GraemePerrins/LEDLamp/FinishedLamp/PXL_20251227_023226788.jpg

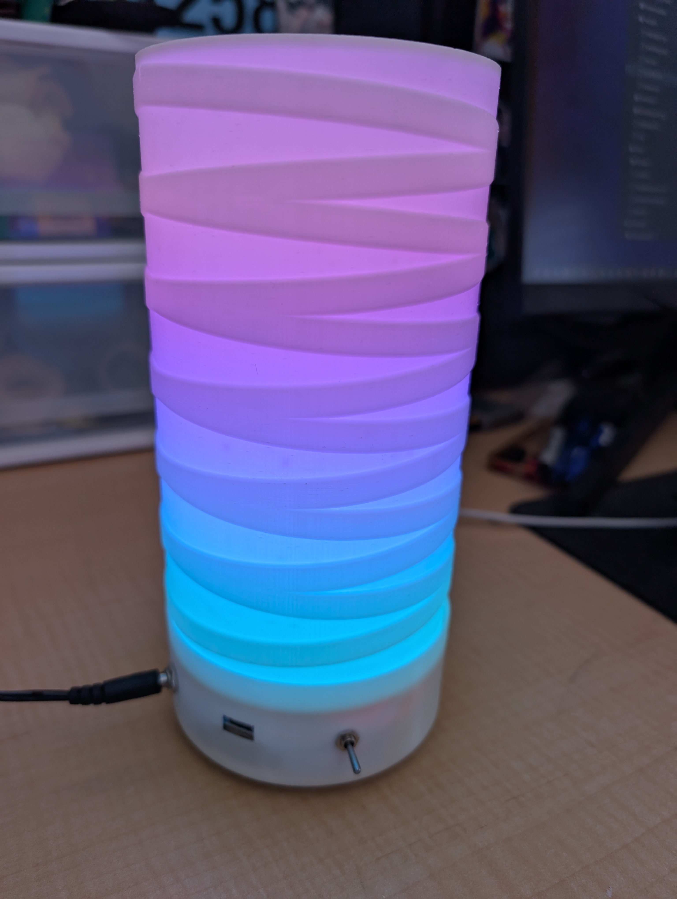
FinishedLamp/PXL_20251227_023226788.jpg
