GraemePerrins/LEDLamp/FinishedLamp/PXL_20251227_023343252.jpg

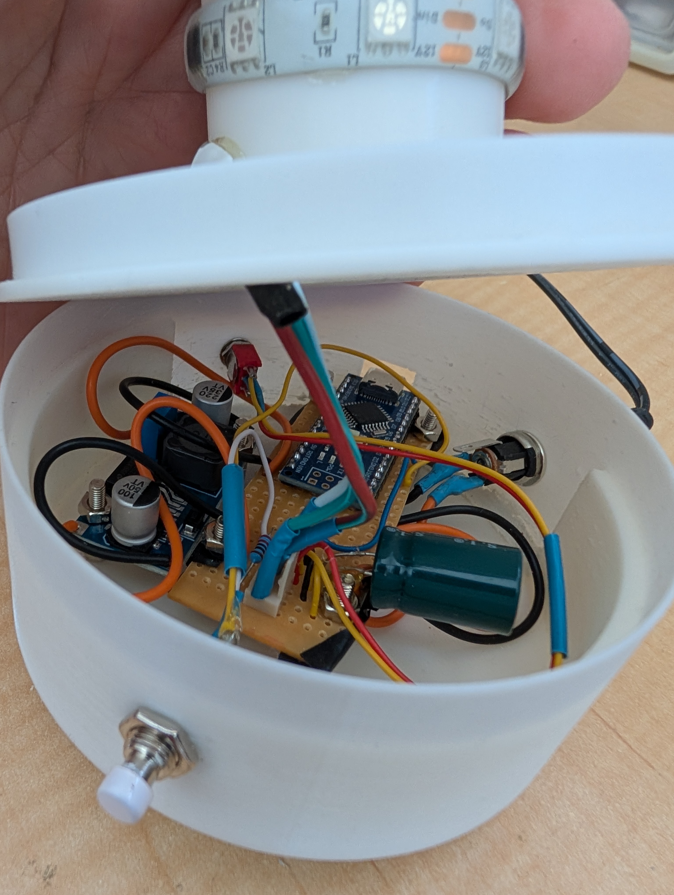
FinishedLamp/PXL_20251227_023343252.jpg
