GraemePerrins/LEDLamp/Arduino/LEDLamp/LEDPatterns.h

#ifndef LP_LEDPATTERN_H
#define LP_LEDPATTERN_H


#include "PinkPurpleCycle.h"
#include "FirePattern.h"
#include "ColourWave.h"
#include "BlueSky.h"
#include "NoisePulse.h"
#include "RandomColour.h"
#include "LavaLamp.h"
#include "WhiteBreath.h"


void initialisePatterns(int numLeds);
void randomShufflePatternIndexes();
void changePattern();
void patternCycle();

#endif
